PaulGoldschmidt/OSAMD/2_Software/Arduino/main/I2C_Chars.ino

unsigned char b;
unsigned int peace;

// Fortschrittsbalken Charaktere:
byte p1[8] = {
  0x10,
  0x10,
  0x10,
  0x10,
  0x10,
  0x10,
  0x10,
  0x10
};

byte p2[8] = {
  0x18,
  0x18,
  0x18,
  0x18,
  0x18,
  0x18,
  0x18,
  0x18
};

byte p3[8] = {
  0x1C,
  0x1C,
  0x1C,
  0x1C,
  0x1C,
  0x1C,
  0x1C,
  0x1C
};

byte p4[8] = {
  0x1E,
  0x1E,
  0x1E,
  0x1E,
  0x1E,
  0x1E,
  0x1E,
  0x1E
};

byte p5[8] = {
  0x1F,
  0x1F,
  0x1F,
  0x1F,
  0x1F,
  0x1F,
  0x1F,
  0x1F
};

void Setup_I2C() {
  lcd.init();
  // i2c-Display intialisieren
  lcd.createChar(0, p1);
  lcd.createChar(1, p2);
  lcd.createChar(2, p3);
  lcd.createChar(3, p4);
  lcd.createChar(4, p5);
  // Hintergrundbeleuchtung an, wenn Variable dafür wahr.
  if (I2C_backlight == true) {
    lcd.backlight();
  }
  else lcd.noBacklight(); 
}

void LCD_Draw(int value) {
  lcd.setCursor(0, 1);

  double a = lengh / 100 * value;

  // drawing black rectangles on LCD

  if (a >= 1) {

    for (int i = 1; i < a; i++) {

      lcd.write(byte(4));

      b = i;
    }

    a = a - b;

  }

  peace = a * 5;

  // drawing charater's colums

  switch (peace) {

    case 0:

      break;

    case 1:
      lcd.write(byte(0));

      break;

    case 2:
      lcd.write(byte(1));
      break;

    case 3:
      lcd.write(byte(2));
      break;

    case 4:
      lcd.write(byte(3));
      break;

  }

  //clearing line
  for (int i = 0; i < (lengh - b); i++) {

    lcd.print(" ");
  }
}
