PaulGoldschmidt/OSAMD/2_Software/Tests/tonegenerator/tonegenerator.ino

const int buzzer = 5; //buzzer to arduino pin 9


void setup(){
 
  pinMode(buzzer, OUTPUT); // Set buzzer - pin 9 as an output

}

void loop(){
 
  tone(buzzer, 440); // Send 1KHz sound signal...
  delay(1000);        // ...for 1 sec
  noTone(buzzer);     // Stop sound...
  delay(1000);        // ...for 1sec
  
}
